msx-solis/msx-fdc-cdx2-clone/cdx-2-iface2.4/kicad/microsol-CDX2-B.jpg

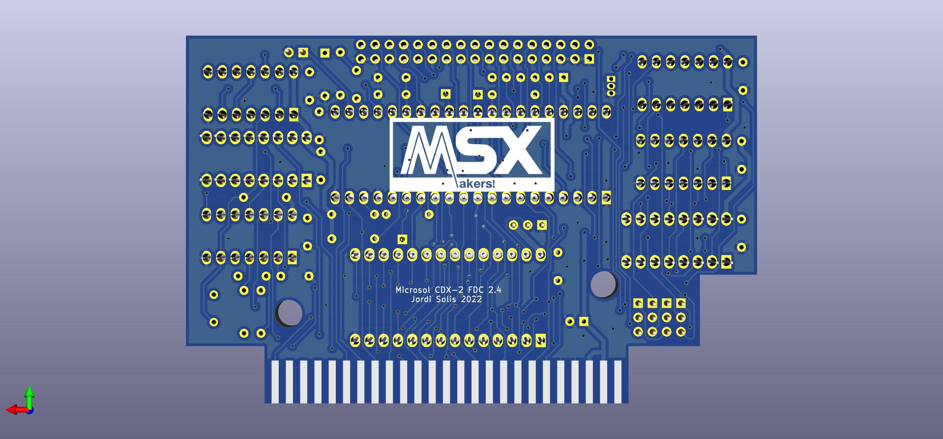
cdx-2-iface2.4/kicad/microsol-CDX2-B.jpg
