msx-solis/msx-fdc-cdx2-clone/cdx-2-iface2.4/pictures/IMG_20230217_1640035.jpg

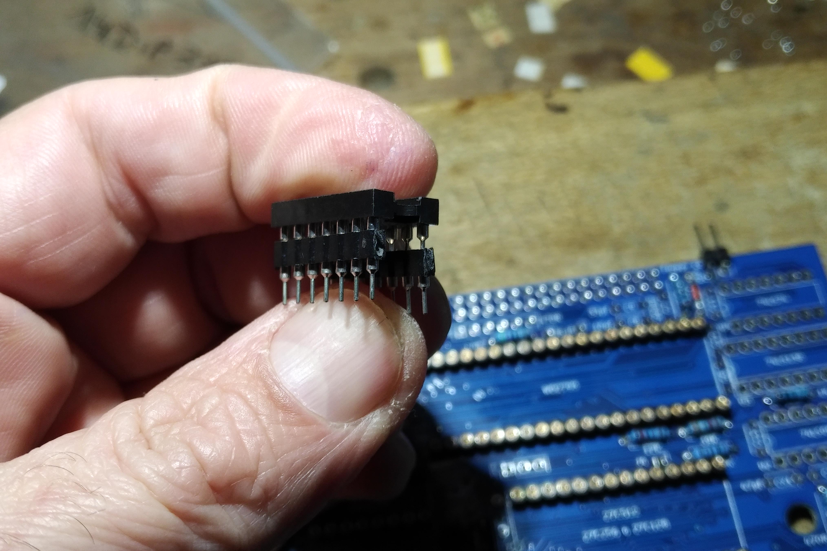
cdx-2-iface2.4/pictures/IMG_20230217_1640035.jpg
