msx-solis/msx-fdc-cdx2-clone/cdx-2-iface2.4/pictures/IMG_20230217_2103335.jpg

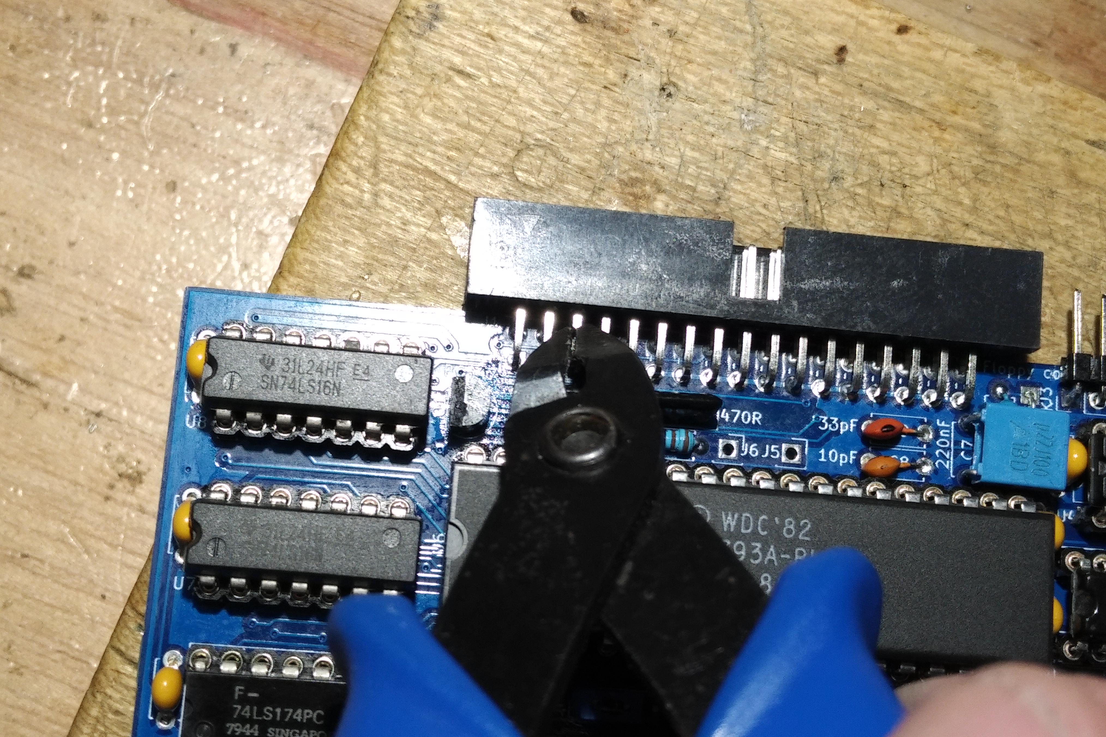
cdx-2-iface2.4/pictures/IMG_20230217_2103335.jpg
