msx-solis/msx-fdc-cdx2-clone/cdx-2-iface2.4/pictures/IMG_20230218_1045268.jpg

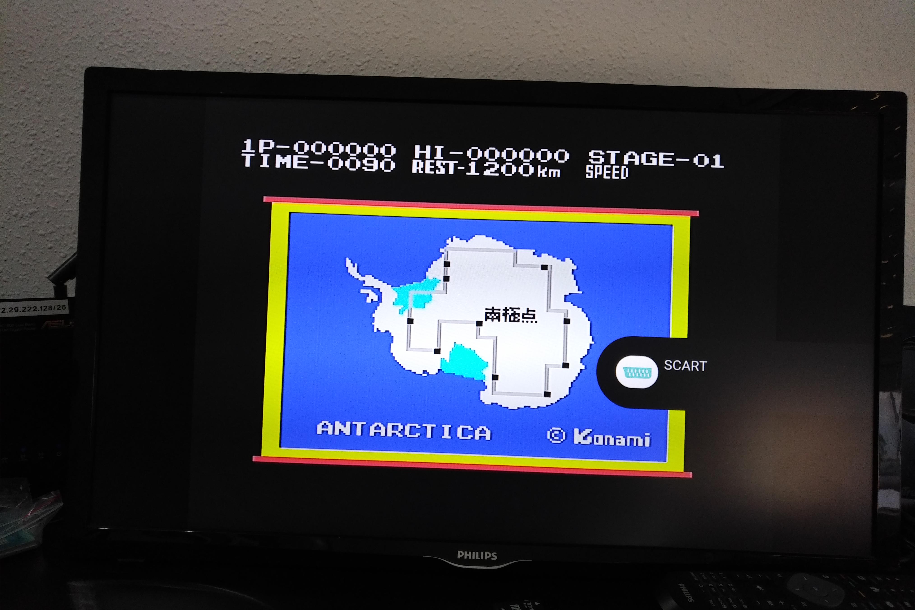
cdx-2-iface2.4/pictures/IMG_20230218_1045268.jpg
